promesoft/KicadJE-SteinerVCF/DSC_0511.JPG

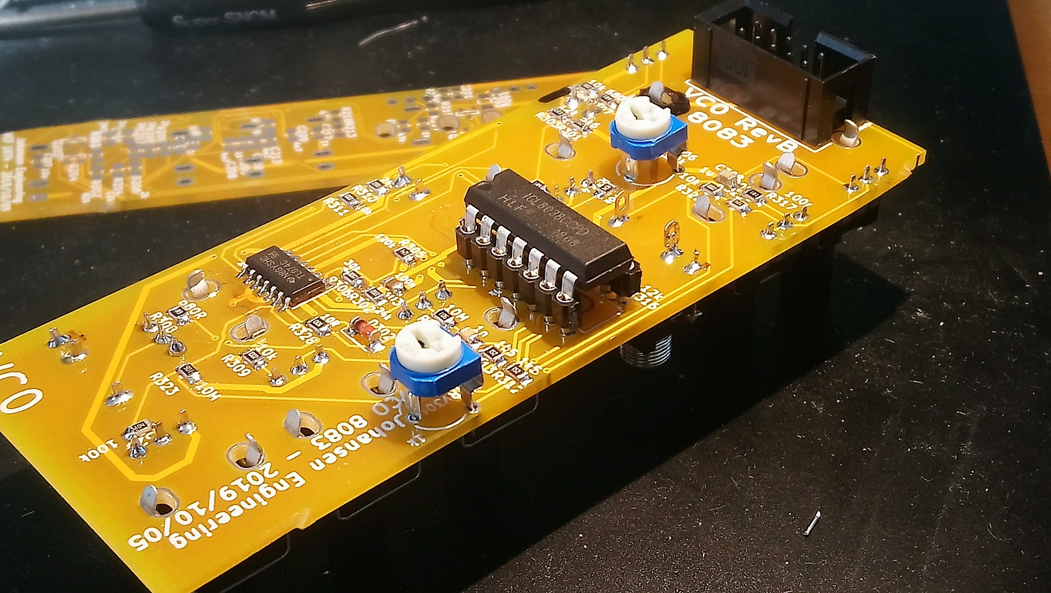
DSC_0511.JPG
