promesoft/KicadJE-SteinerVCF/DSC_2366.JPG

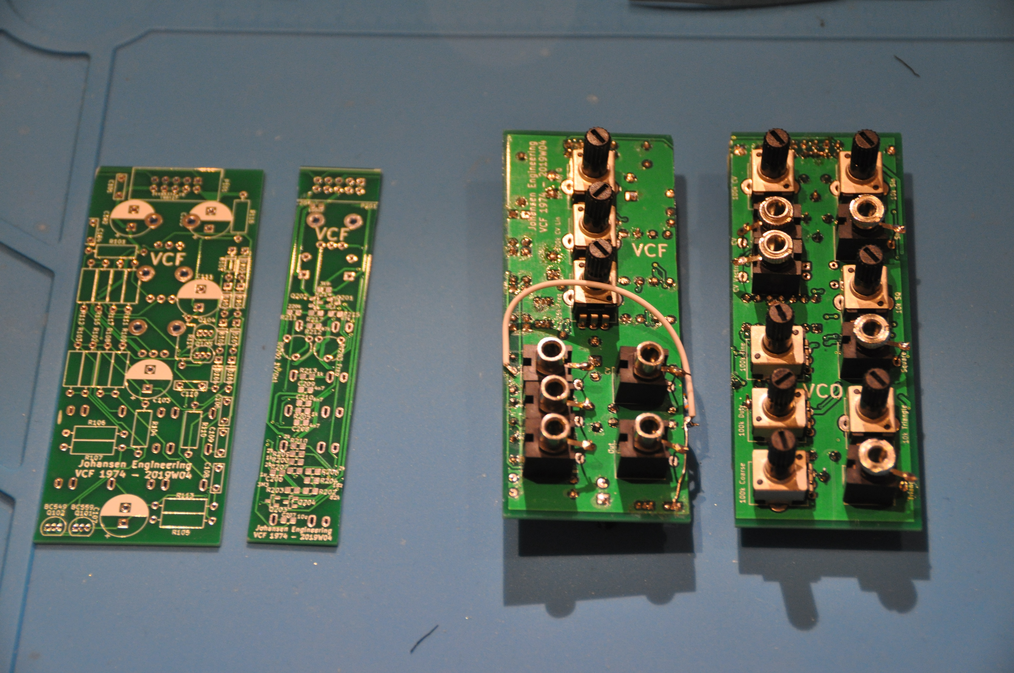
DSC_2366.JPG
