promesoft/KicadJE-SteinerVCF/DSC_2367.JPG

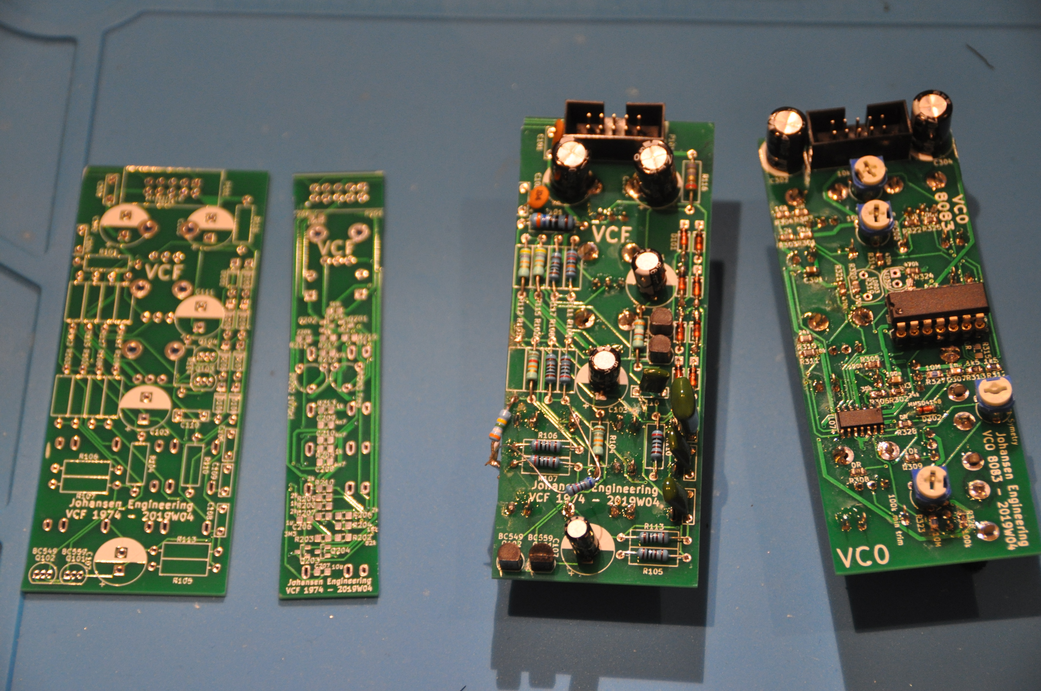
DSC_2367.JPG
