promesoft/KicadJE-SteinerVCF/Kicad-JE-SteinerVCF-1974-TopRevA2.png

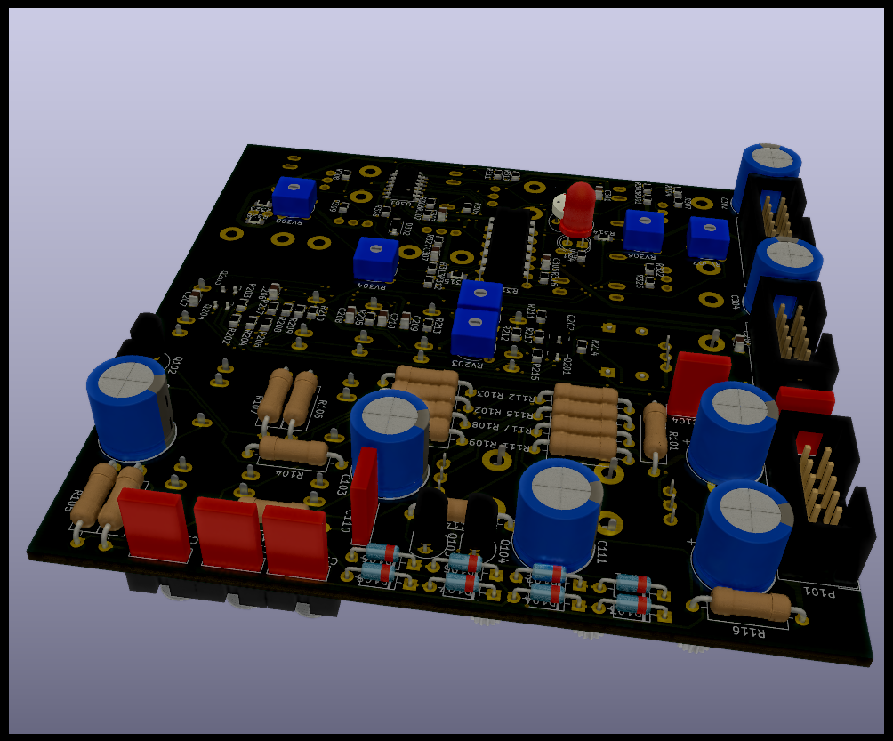
Kicad-JE-SteinerVCF-1974-TopRevA2.png
