promesoft/KicadJE-SteinerVCF/Kicad-JE-SteinerVCF-1974-TopRevA.png

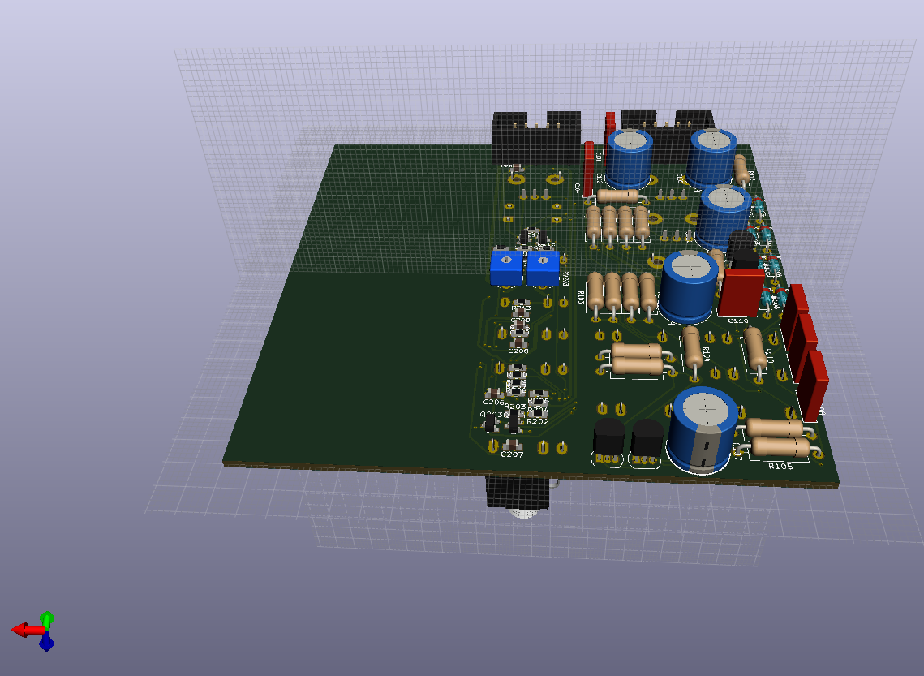
Kicad-JE-SteinerVCF-1974-TopRevA.png
