promesoft/KicadJE-SteinerVCF/MIDI out TNCq2.png

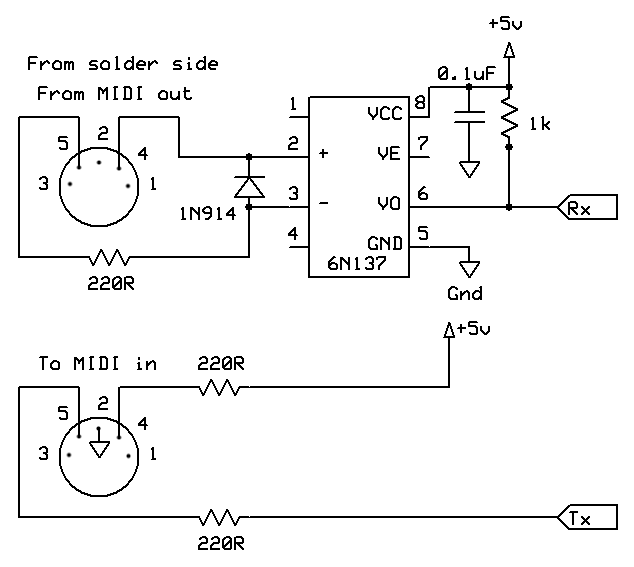
MIDI out TNCq2.png
