promesoft/KicadJE-SteinerVCF/roland.TB-303.schem-5.gif

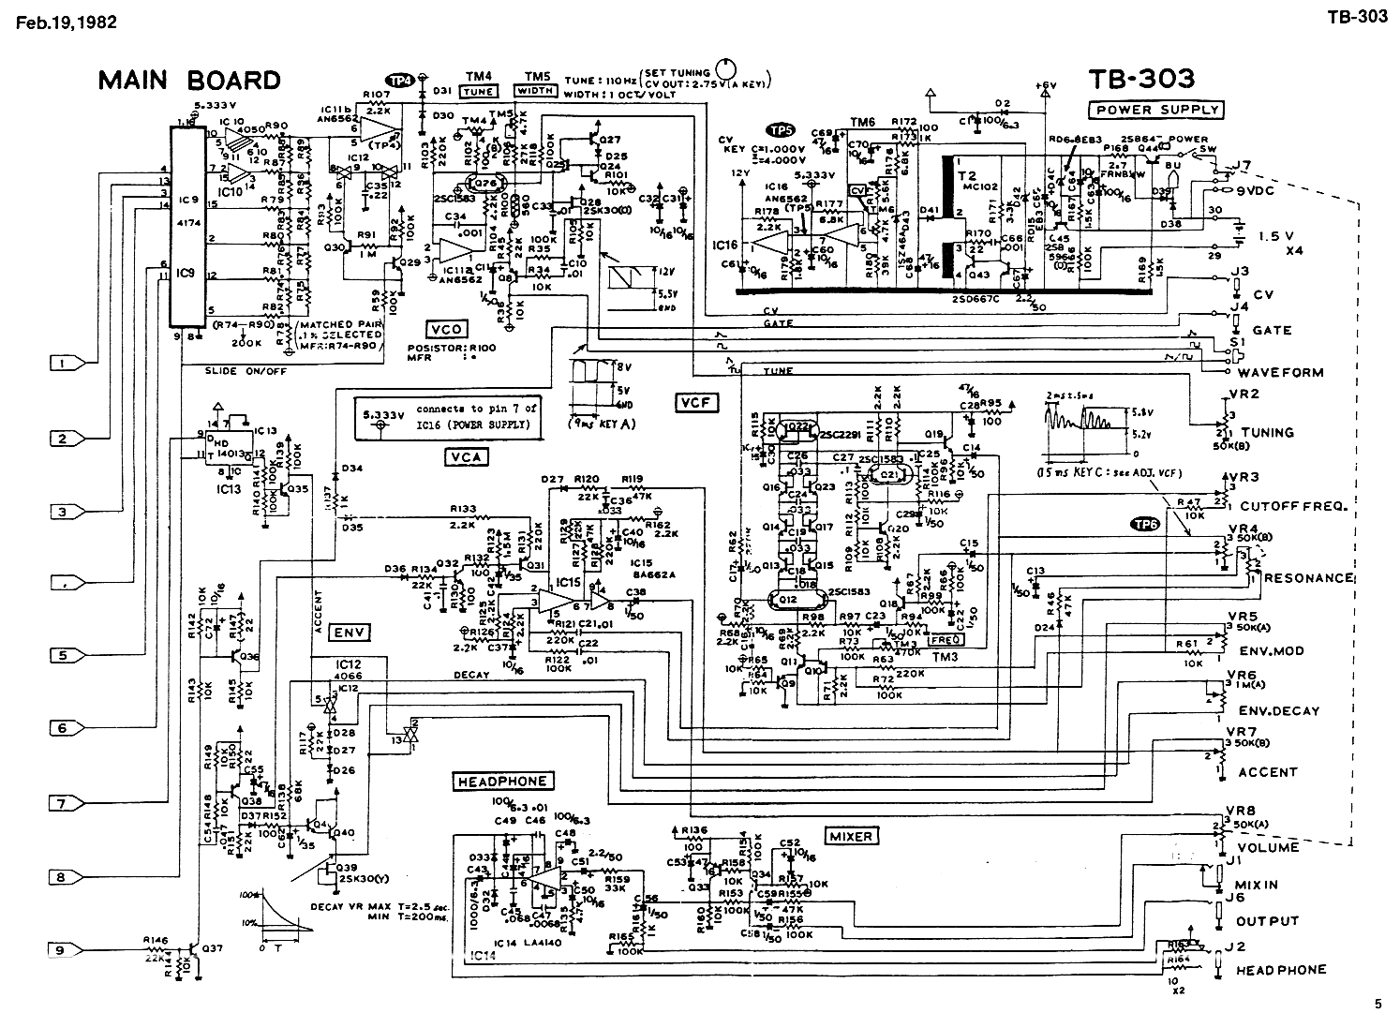
roland.TB-303.schem-5.gif
