promesoft/KicadJE-SteinerVCF/s100m02a.jpg

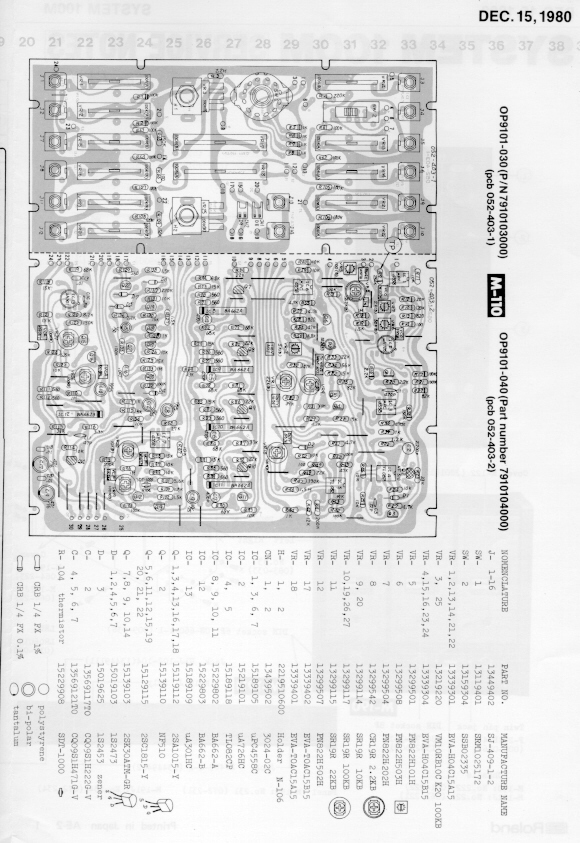
s100m02a.jpg
