promesoft/KicadJE-SteinerVCF/VCA_Diagram_135-10430.png

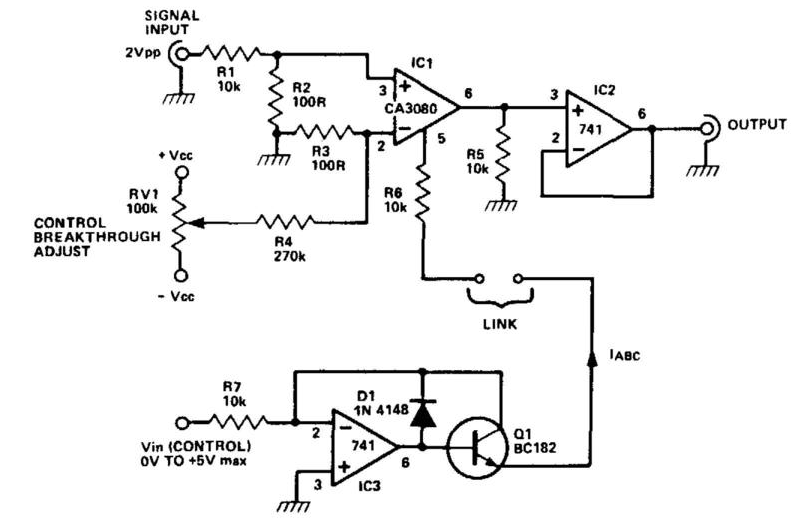
VCA_Diagram_135-10430.png
