promesoft/KicadJE-SteinerVCF/VCO_8083_2019_03.JPG

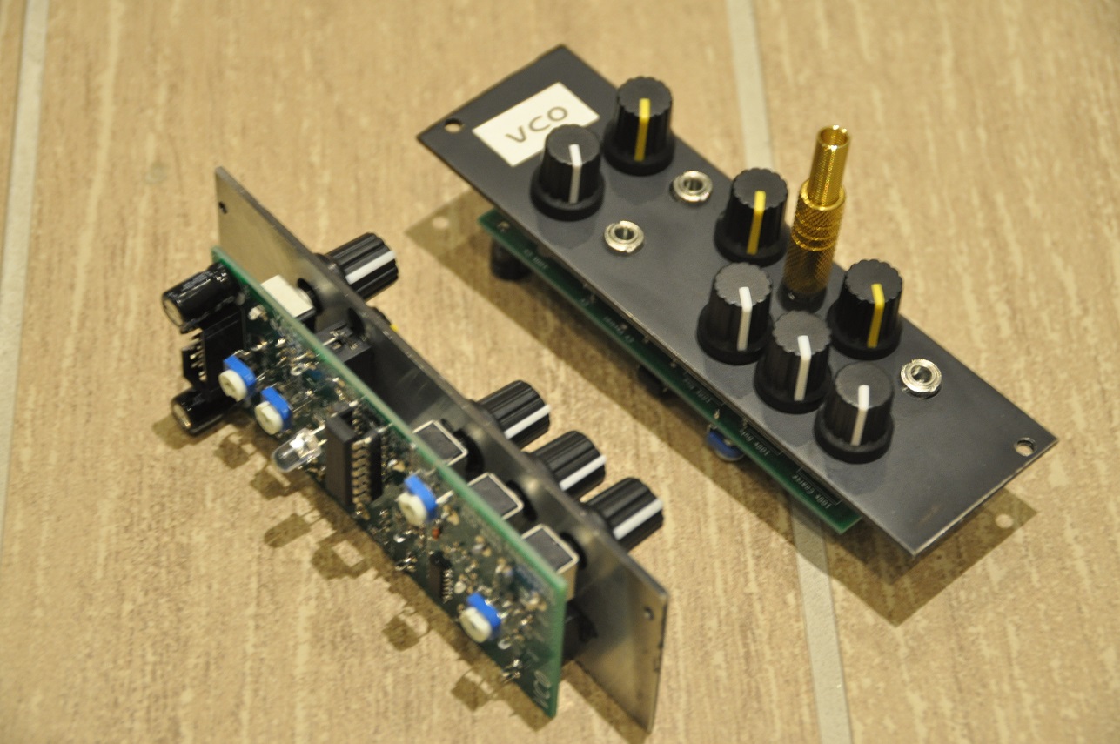
VCO_8083_2019_03.JPG
